stkdiretto/uulmduino/handbuch/img_uulm/fertig_frontal.jpg

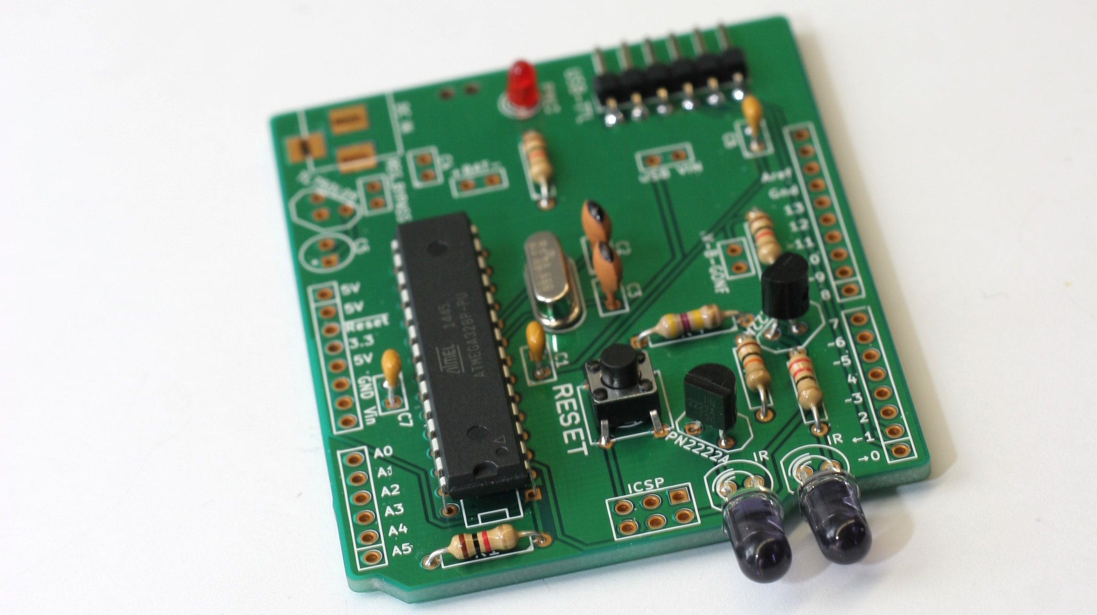
handbuch/img_uulm/fertig_frontal.jpg
